NurRohmatHidayat/Smart-Building-Solution/Dokumentasi/Asemmbly.png

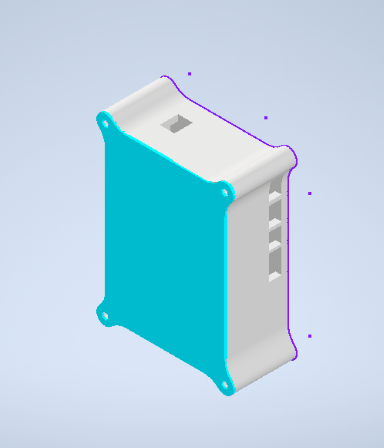
Dokumentasi/Asemmbly.png
