NurRohmatHidayat/Smart-Building-Solution/Dokumentasi/Cetak 3D.jpg

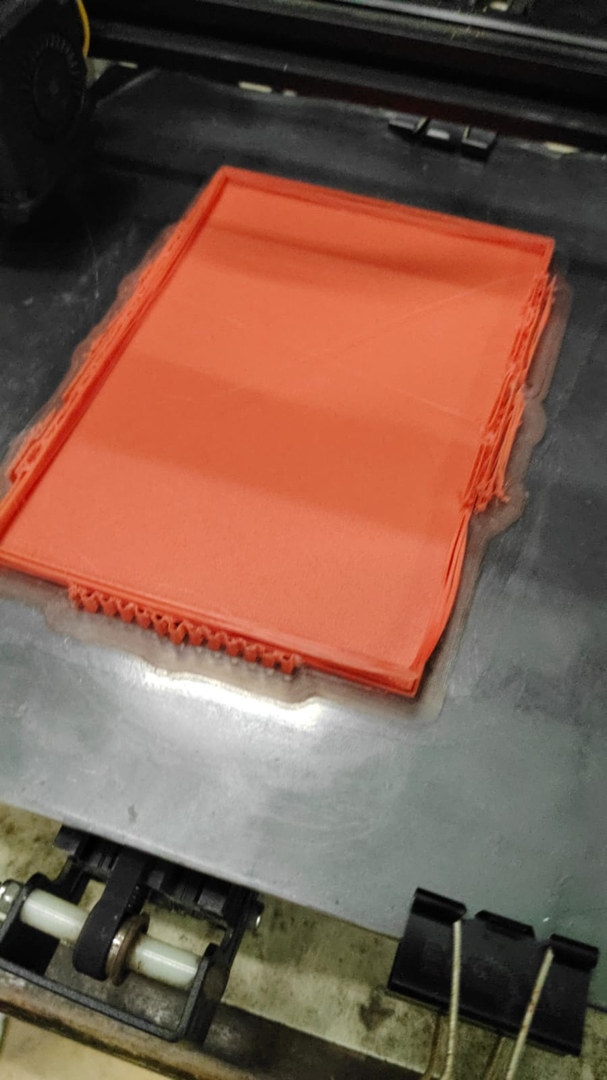
Dokumentasi/Cetak 3D.jpg
