NurRohmatHidayat/Smart-Building-Solution/Dokumentasi/Prototype.jpg

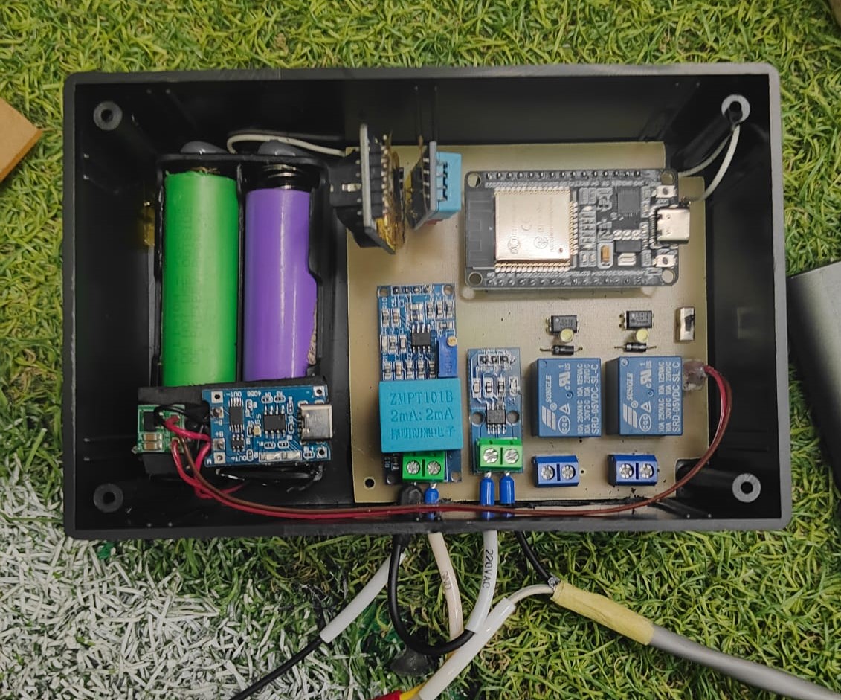
Dokumentasi/Prototype.jpg
