NurRohmatHidayat/Smart-Building-Solution/Dokumentasi/Rangkaian Modul ESP32.jpg

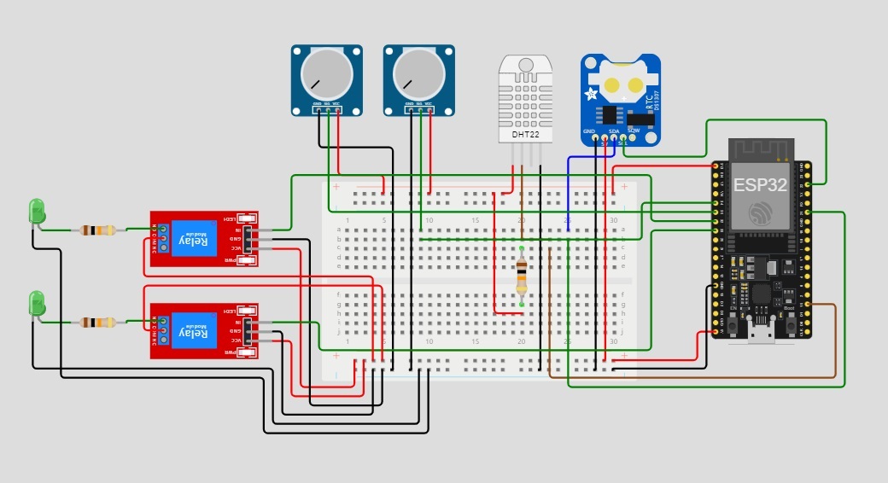
Dokumentasi/Rangkaian Modul ESP32.jpg
